AcubeSAT/satellite-s-band-antenna/Anechoic Chamber Tests/Plots (PDF)/patch_polarization_loss.pdf

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

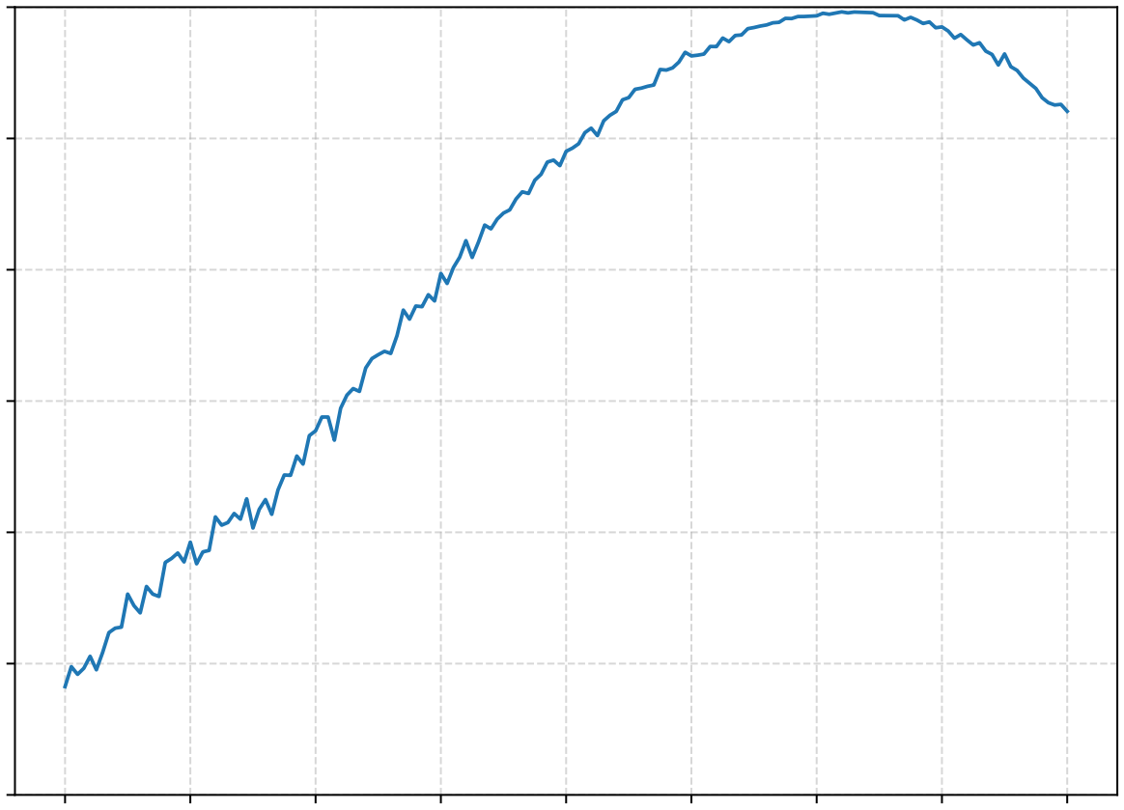
[picture p7: figure]
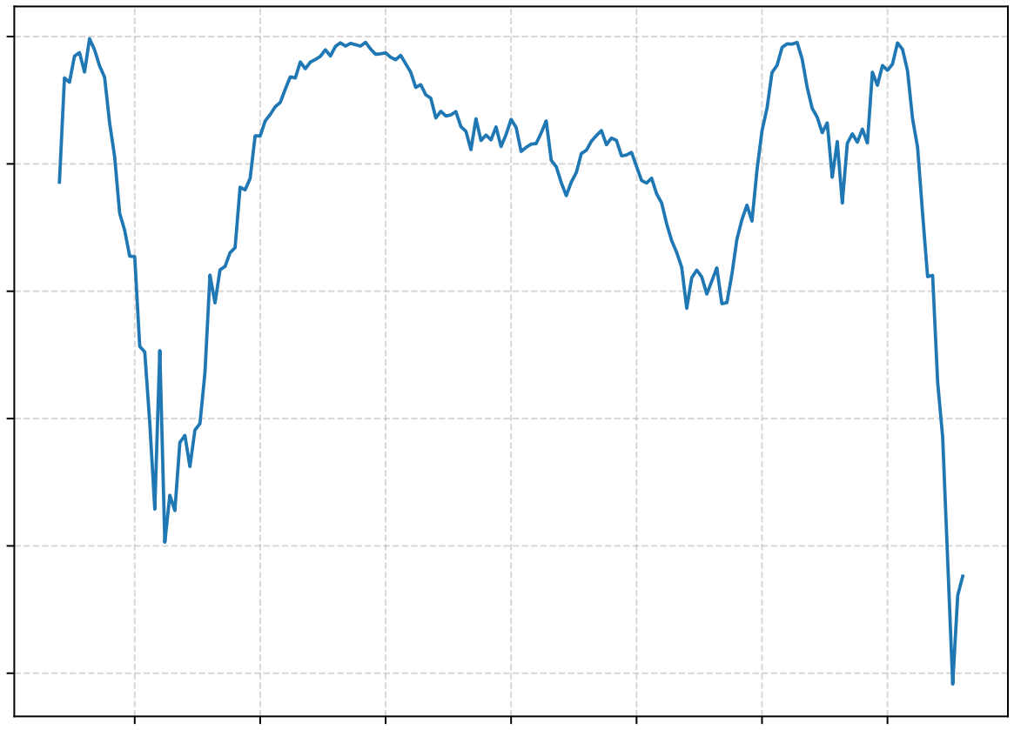
[picture p8: figure]
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
