AcubeSAT/satellite-s-band-antenna/Anechoic Chamber Tests/Plots (PDF)/patch_phase_difference.pdf

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

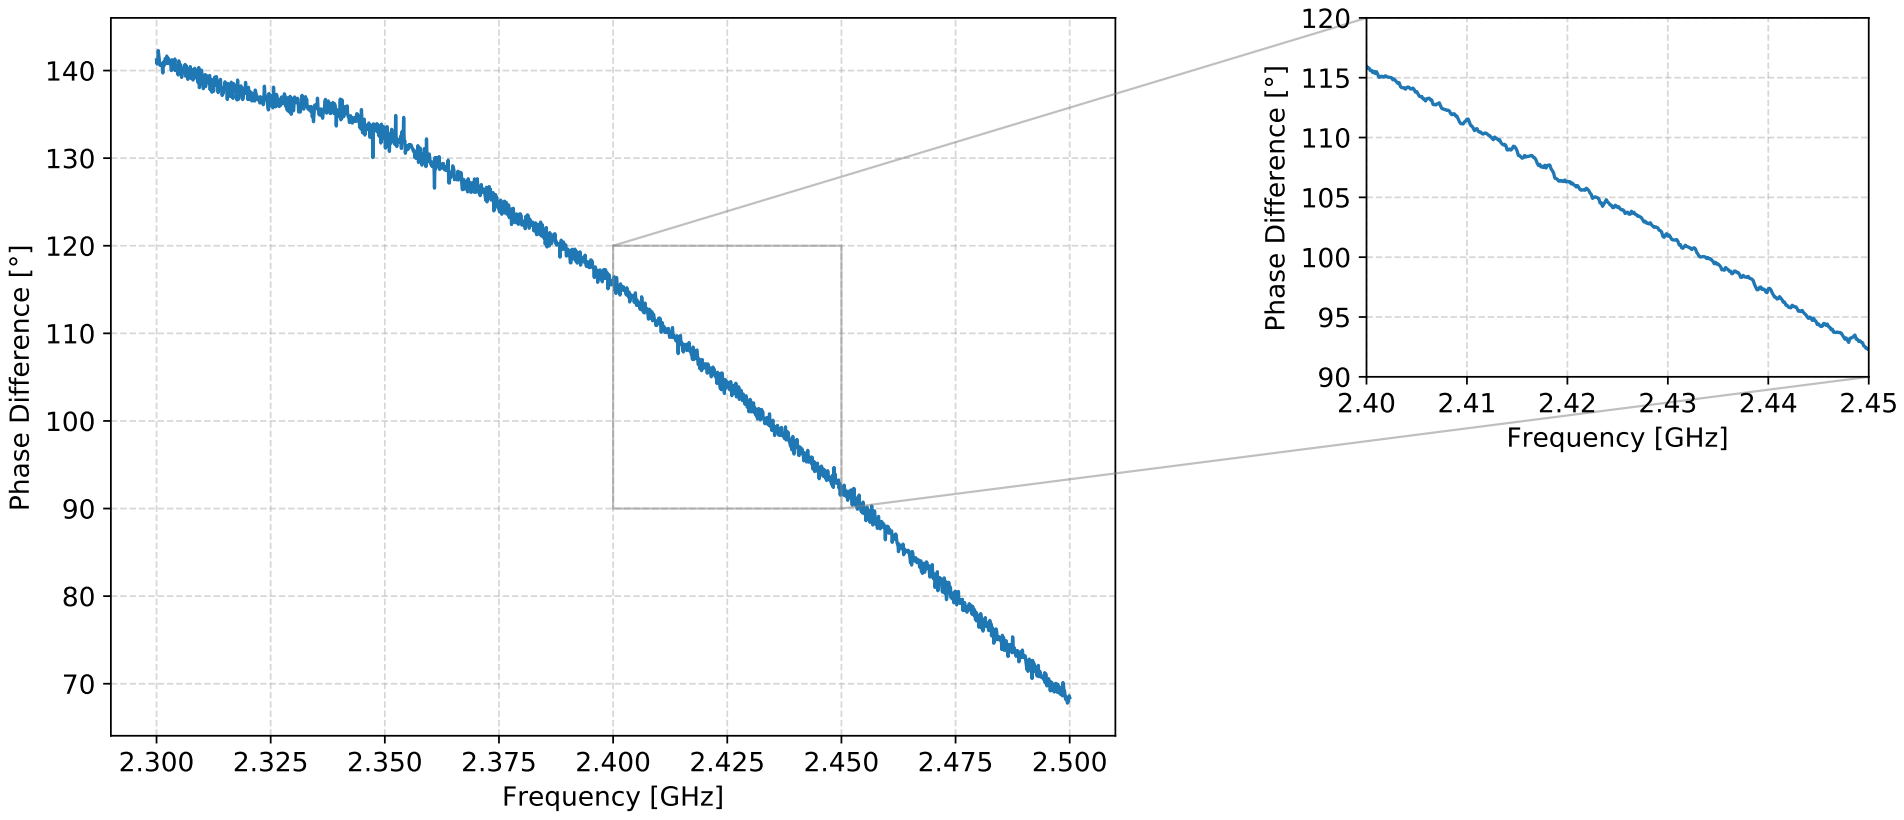
[picture p19: page 1]
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
